ParRot-3DMouse/ParRotHardware/1.0/doc/img/cable/cable.jpg

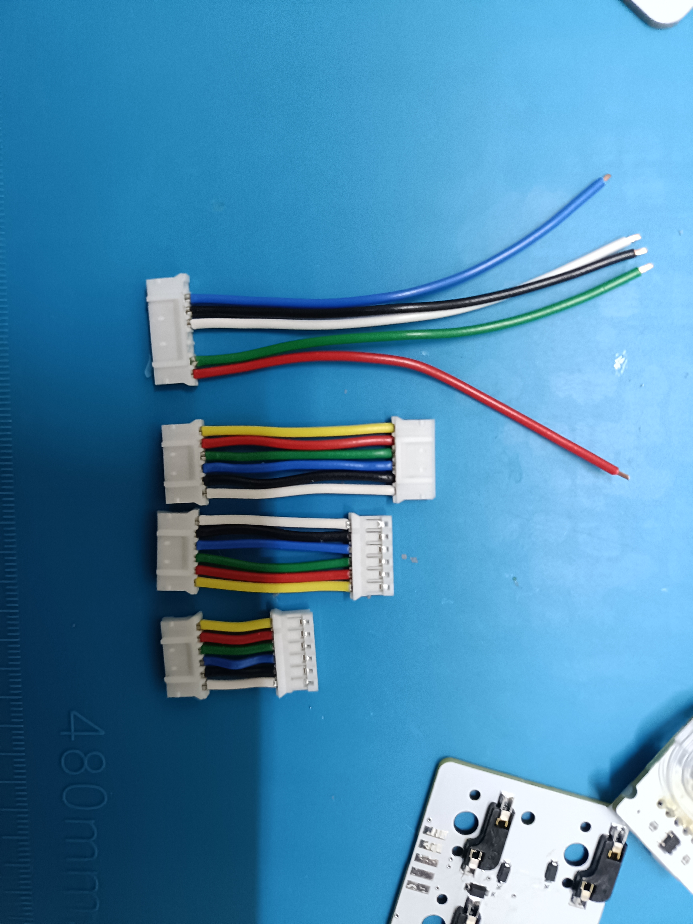
1.0/doc/img/cable/cable.jpg
